Mathesar/a500-mitsumi-keyboard-controller-redone/firmware.X/matrix.c

/*
 *  A500-Mitsumi-controller-redone firmware
 * 
 *  By Dennis van Weeren (2026)
 *  
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
 *  You should have received a copy of the GNU General Public License
 *  along with A500-Mitsumi-controller-redone.  
 *  If not, see <https://www.gnu.org/licenses/>.
 */

#include <xc.h>
#include "matrix.h"
#include "keyboard.h"
#include "main.h"

// key state structure
struct
{
    uint8_t key_states[MATRIX_N_ROWS];
    uint8_t matrix_previous[MATRIX_N_ROWS];
    bool caps_lock_state;
} key_state;

uint8_t matrix[MATRIX_N_ROWS];

// matrix to key code mapping
const uint8_t matrix_to_code_map[MATRIX_N_ROWS][MATRIX_N_COLS] = 
{
//      2     4     1     0     5     3   extra     (column)
    { 0x4f, 0x4d, 0x4c, 0x5f, 0x4a, 0x4e, 0x00 },   // row 0
    { 0x44, 0x41, 0x0d, 0x59, 0x0f, 0x46, 0x00 },   // row 1
    { 0x1b, 0x40, 0x0c, 0x58, 0x1d, 0x2b, 0x00 },   // row 2
    { 0x1a, 0x00, 0x0b, 0x57, 0x2d, 0x2a, 0x00 },   // row 3
    { 0x19, 0x3a, 0x0a, 0x56, 0x3d, 0x29, 0x00 },   // row 4
    { 0x18, 0x39, 0x09, 0x5c, 0x43, 0x28, 0x00 },   // row 5
    { 0x17, 0x38, 0x08, 0x55, 0x1e, 0x27, 0x00 },   // row 6
    { 0x16, 0x37, 0x07, 0x5b, 0x2e, 0x26, 0x00 },   // row 7
    { 0x15, 0x36, 0x06, 0x54, 0x3e, 0x25, 0x00 },   // row 8
    { 0x14, 0x35, 0x05, 0x53, 0x3c, 0x24, 0x00 },   // row 9
    { 0x13, 0x34, 0x04, 0x52, 0x1f, 0x23, 0x00 },   // row 10
    { 0x12, 0x33, 0x03, 0x51, 0x2f, 0x22, 0x00 },   // row 11
    { 0x11, 0x32, 0x02, 0x50, 0x3f, 0x21, 0x00 },   // row 12
    { 0x10, 0x31, 0x01, 0x5a, 0x5e, 0x20, 0x00 },   // row 13
    { 0x42, 0x30, 0x00, 0x45, 0x5d, 0x62, 0x00 },   // row 14
    { 0x66, 0x64, 0x60, 0x63, 0x65, 0x61, 0x67 }    // row 15 (extra)
};

// CAPS-LOCK key code
#define CAPS_LOCK_CODE  0x62

//select a row by pulling the output low
void matrix_select_row(uint8_t row)
{
    switch(row)
    {
        case 0:     MATRIX_Y0=0;    break;
        case 1:     MATRIX_Y1=0;    break;
        case 2:     MATRIX_Y2=0;    break;
        case 3:     MATRIX_Y3=0;    break;
        case 4:     MATRIX_Y4=0;    break;
        case 5:     MATRIX_Y5=0;    break;
        case 6:     MATRIX_Y6=0;    break;
        case 7:     MATRIX_Y7=0;    break;
        case 8:     MATRIX_Y8=0;    break;
        case 9:     MATRIX_Y9=0;    break;
        case 10:    MATRIX_Y10=0;   break;
        case 11:    MATRIX_Y11=0;   break;
        case 12:    MATRIX_Y12=0;   break;
        case 13:    MATRIX_Y13=0;   break;
        default:    MATRIX_Y14=0;   break;        
    }
}

//deselect a row by making the output high-z
void matrix_deselect_row(uint8_t row)
{
    switch(row)
    {
        case 0:     MATRIX_Y0=1;    break;
        case 1:     MATRIX_Y1=1;    break;
        case 2:     MATRIX_Y2=1;    break;
        case 3:     MATRIX_Y3=1;    break;
        case 4:     MATRIX_Y4=1;    break;
        case 5:     MATRIX_Y5=1;    break;
        case 6:     MATRIX_Y6=1;    break;
        case 7:     MATRIX_Y7=1;    break;
        case 8:     MATRIX_Y8=1;    break;
        case 9:     MATRIX_Y9=1;    break;
        case 10:    MATRIX_Y10=1;   break;
        case 11:    MATRIX_Y11=1;   break;
        case 12:    MATRIX_Y12=1;   break;
        case 13:    MATRIX_Y13=1;   break;
        default:    MATRIX_Y14=1;   break;        
    }
}

// return status of matrix columns
// if a key was pressed the corresponding column bit is set
uint8_t matrix_read_columns(void)
{
    uint8_t columns = (PORTA & 0x0f) ^ 0x0f;
    if(PORTBbits.RB6 == 0)
        columns |= 0x10;
    if(PORTBbits.RB7 == 0)
        columns |= 0x20;
         
    return columns;
}

// count the number of bits set in a byte using Brian Kernighan's Algorithm
uint8_t matrix_count_bits_set(uint8_t value)
{
    uint8_t bits_set; // number of bits set counter
    for (bits_set = 0; value; bits_set++)
    {
      value &= value - 1; // clear the least significant bit set
    }    
    
    return bits_set;
}

// Toggle CAPS-LOCK on or off
// returns correct key code
uint8_t matrix_handle_caps_lock(void)
{
    if(key_state.caps_lock_state)
    {
        // turn caps lock off
        key_state.caps_lock_state = false;
        CAPS_LOCK = 1;
        return CAPS_LOCK_CODE | 0x80;
    }
    else
    {
        // turn caps lock on
        key_state.caps_lock_state = true;
        CAPS_LOCK = 0;
        return CAPS_LOCK_CODE;
    }     
}

// check for ghosting
bool matrix_check_ghosting(void)
{    
    for(uint8_t row = 0; row < MATRIX_N_ROWS-1; row++)
    {
        // if there is any row with more than 1 column set
        // and these columns overlap with a colum in any 
        // other row we have ghosting
        uint8_t columns = matrix[row];        
        if( matrix_count_bits_set(columns) > 1 )
        {
            // >1 column set, check against other rows
            for(uint8_t x = 0; x < MATRIX_N_ROWS-1; x++)
            {                
                if(x != row)
                {
                    if(columns & matrix[x])
                    {
#ifndef NDEBUG
                        printf("ghosting!\n");
#endif
                        // overlap! ghosting detected
                        return true;
                    }                       
                }
            }    
        }        
    }
    
    // no ghosting
    return false;
}

// Scan the matrix and place the scanned matrix in global <matrix>.
void matrix_scan(void)
{
    uint8_t row, columns;
   
    for(row=0; row<MATRIX_N_ROWS-1; row++)
    {
        // scan regular matrix row
        matrix_select_row(row);
        
        // allow 40us for row to settle
        us_timer_set(40);
        us_timer_wait();

        // read pressed keys for this row
        columns = matrix_read_columns();   
        
        // deselect row
        matrix_deselect_row(row);
        
        // allow 160us for row to clear
        us_timer_set(160);
        us_timer_wait();

        // store result for this row
        matrix[row] = columns;
    }
    
    // scan special keys and put them in the extra row
    columns = 0;
    if(LEFT_AMIGA == 0)
        columns |= 0x01;
    if(LEFT_ALT == 0)
        columns |= 0x02;
    if(LEFT_SHIFT == 0)
        columns |= 0x04;
    if(CTRL == 0)
        columns |= 0x08;
    if(RIGHT_ALT == 0)
        columns |= 0x10;
    if(RIGHT_SHIFT == 0)
        columns |= 0x20;
    if(RIGHT_AMIGA == 0)
        columns |= 0x40;
    matrix[row] = columns;    
}

// Takes the scanned matrix in global <matrix>, checks for ghosting,
// performs debouncing and scans for key pressed / released events.
// Events are pushed into the keyboard buffer.
void matrix_decode(void)
{ 
    uint8_t n = 0;
    
    // if matrix is ghosting
    // do not decode matrix
    if(matrix_check_ghosting())
        return;

    // go through all rows
    for(uint8_t row=0; row<MATRIX_N_ROWS; row++)
    {               
        uint8_t current = matrix[row];
        uint8_t previous = key_state.matrix_previous[row];
        key_state.matrix_previous[row] = current;        
        uint8_t state = key_state.key_states[row];
        
        // for proper debouncing, keys must be pressed or released for 
        // at least 2 consecutive scans in order to be registered
        uint8_t pressed  =  (current & previous) & ~state;
        uint8_t released = ~(current | previous) &  state;     
 
        if(pressed|released)
        {
            // event(s) detected, update key states
            key_state.key_states[row] ^= pressed | released;

            // go through all columns
            uint8_t column_mask = 1;
            for(uint8_t column=0; column<MATRIX_N_COLS; column++)
            {                         
                uint8_t code = matrix_to_code_map[row][column];
                    
                if(pressed&column_mask)
                {
                    if(code == CAPS_LOCK_CODE)
                    {
                        // CAPS-LOCK is special, toggles on "pressed" events
                        code =  matrix_handle_caps_lock();
                    }
                    
                    keyboard_put_buffer(code);
#ifndef NDEBUG
                    printf("[%u,%u] DOWN, CODE:0x%02X\n", row, column, code);
#endif
                }
                else if(released&column_mask)
                {            
                    if(code != CAPS_LOCK_CODE)
                    {
                        keyboard_put_buffer(code|0x80);     
#ifndef NDEBUG
                        printf("[%u,%u] UP, CODE:0x%02X\n", row, column, code);
#endif
                    }
                }

                // next column
                column_mask <<= 1;
            }    
        }
    } 
}
